Hustlenix/Nightwave/docs/expanded-software-checkpoint.md

# Final-master execution checkpoint

2026-10-03 current continuation: BM83SM1-00TA and Waveshare 24382 non-touch selected.
BD-16 selects TCA9535PWR input expansion; combined map and reviewed charger/pack/
BT rail remain open. The
following historical ledger is superseded for MP3 duration/sparse seek, portable
BT/power/display interfaces and engineering JSON by mp3-seek-index.md and
software-interfaces.md. Actual current-revision CI is in software-validation.md.

2026-10-01. This document is a completion ledger, not a claim that everything
is finished. Existing history is preserved. No final hardware source was
AI-authored, no orders were placed and no human hours/results were invented.

| Requested feature | Actual checkpoint | Remaining acceptance |
| --- | --- | --- |
| Direct microSD MP3/WAV | Existing real three-task engine retained | Real SD/decoder/output latency and hot-remove recovery |
| Lyrics | Bounded LRC loader and current/next OLED view; sample clock | Acoustic alignment, wrapping/Unicode on chosen display |
| Metadata | ID3v2.3/v2.4/v1 and WAV INFO; PCM duration | MP3 duration/index, unsupported tag variants |
| Library | Idle-built SD catalog, 16-row pages, PSRAM artist/album lookup and direct filtered track access; folder/M3U | Metadata reuse; slow fallback/SD contention and real card latency acceptance |
| Modes | Normal/shuffle/repeat-all/repeat-track; EOF advance | Long on-board mixed-media stress |
| Resume | Checked NVS; explicit M3U/folder/index context; checked ordinal hint, legacy/stale fallback | Fast MP3 seek, browser cursor, missing-cache context reconstruction |
| Sleep | Off/15/30/45/60/end-track; pause ramp, stop, display sleep | Measured low power / physical master shutdown |
| Outputs | Speaker/wired/auto preference, faded switch | Chosen Bluetooth transport; actual jack circuit |
| Battery | Unknown/unmeasured displayed honestly | Gauge/bus HAL, charging/fault/low-battery shutdown after power choice |
| Diagnostics | JSON boot/stream/performance/self-test + parser | Task CPU, route counters, BT/battery telemetry, physical evidence |
| Display | Bench OLED; selected 24382 geometry/tile contract | Combined GPIO review, true TFT driver/UI/glyph/current/fit testing |
| Engineering/manufacturing | Updated budgets and source-review gates | Complete BOM, builder sources, ERC/DRC/fit/exports, human review |

## Current validation

At 35b7ab4: [device build](https://github.com/Hustlenix/Nightwave/actions/runs/36878328683)
and [Project quality](https://github.com/Hustlenix/Nightwave/actions/runs/36878328795)
succeeded. Seven suites passed in Release and again with AddressSanitizer/leak
detection, including actual LRC/metadata/playlist sources and 1000 parser/shuffle
cycles. Original fixtures are generated locally/in CI, never copyrighted songs
or lyrics. Host scheduling/drivers are simulated, not hardware measurements.

Later source changes require their own successful run; see software-validation.md.
The 2026-10-02 catalog continuation is described in library-index.md; its source
requires a new device/host run before reusing the older validation claims below.
At 630e3ec device compilation passed; its new playlist-resume assertion failed
with a noncanonical host fixture root. Canonicalised fixtures and isolated
generated-playlist cleanup address that regression; rerun evidence is recorded
only after execution. A targeted frontend test also passed locally in Ubuntu WSL.

Latest validated source: 50df90c device build/size reports and 92c17ea Project
quality, both successful. Seven Release + seven ASAN/leak suites passed. The
targeted frontend/media suites passed ASAN/leak detection locally in WSL too.
See software-validation.md for exact run links and limits; firmware source has
not changed after 50df90c. Future documentation-only evidence commits do not
change the built firmware.
Initial 54ba552 tests caught corrupt-path display clipping; repaired in 35b7ab4.
Do not hide a failed run or treat an unexecuted checklist as a pass.

Current 2026-10-02 checkpoint: 14b10c0 [device build/size](https://github.com/Hustlenix/Nightwave/actions/runs/36962788706)
and [8/8 Release + 8/8 ASAN/leak suites](https://github.com/Hustlenix/Nightwave/actions/runs/36962788677)
passed. This supersedes the older firmware-source/evidence paragraph above.
The catalog and real frontend integrate >128-track fixtures, full indexed/filter
queues and resume. Later v2 lookup source has separate evidence in
software-validation.md; old slow scans remain a declared fallback, not the
normal accelerated group/filter path.
No physical SD, acoustic, battery or hardware-authorship result follows from CI.

## Actual next human gate

BD-14 selects S3 + BM83SM1-00TA, BD-15 selects Waveshare 24382 non-touch and
BD-16 selects TCA9535PWR input expansion. The choices are recorded, but final
schematic/PCB/CAD cannot start until current software is pushed/verified and the
combined numbered map, power/charger/pack/BT rail and support BOM are reviewed.
Selected SKU does not mean functioning radio/display or reviewed drawing.

After the recorded BD-15 choice: reconcile GPIO/SRAM/PSRAM/power and implement exact selected
adapters/display UI. MP3 duration/seek and portable HAL contracts are implemented;
vendor firmware access, rate conversion and physical power adapters remain open. Then
builder authors one subsystem at a time using builder-tasks.md. Reviews identify
specific issues, builder fixes and returns sources; independent human review
and actual manufacturing exports remain hard funding blockers.
