Hustlenix/Nightwave/docs/pixl-funding-readiness.md

# Pixl design/funding requirements

Checked: 2026-10-02 (Asia/Calcutta). This is a design-stage audit, not approval.

Official sources:

- https://pixl.hackclub.com/docs/hardware-requirements
- https://pixl.hackclub.com/docs/submitting
- https://pixl.hackclub.com/docs/first-project
- https://pixl.hackclub.com/docs/sidequest
- https://pixl.hackclub.com/docs/shipping

## Required before design/funding submission

The hardware-specific page distinguishes digital design funding from later build
submission. It requires an understandable README, assembly/PCB images, a finished
replicable design, complete electronics-inclusive CAD with real attachment
methods, firmware source even if untested, linked BOM CSV with total, PCB sources,
STEP and editable CAD sources, and organized relevant files. Another person must
sanity-check the design and their findings must be addressed.

Authorship is mandatory: the design must be original and by the builder, not AI.
The page warns fully AI-generated design files may be permanently rejected.
AI disclosure and clicking approval on AI output cannot be assumed sufficient.
Builder-created electrical/mechanical work and its provenance are still needed;
obtain program guidance if the proposed assistance boundary is unclear.

2026-10-01 continuation: the builder reports direct clarification from Pixl
permitting AI tutor/second-pair-of-eyes assistance while the builder performs
actual schematic/board engineering and makes final decisions. This is reported
by the user, not independently verified correspondence. Follow the specific
builder-authored workflow in builder-tasks.md; research and software continue
while sources are pending. It does not waive source completeness or review.

## Required later for final build submission

The hardware page additionally requires genuine build-progress journals/photos,
finished-build photos and demo video in README, and source changes matching any
assembly bodges. The general submission pages require tracked human work,
journals, demo and AI notes. Do not substitute a design render for a build photo.

## Nightwave status

Public repo verified through GitHub: https://github.com/Hustlenix/Nightwave.
Existing firmware builds and host tests are software evidence only. No physical
playback, runtime, battery/current, thermal or fit results have been returned.

Project URL: https://pixl.hackclub.com/project/1200. The authenticated Chrome
builder session was inspected on 2026-10-02. It is a hardware funding draft with
finished-built-hardware unchecked. Its Trial requires local files, real speakers,
physical playback/volume controls and a full-night battery with actual runtime
stated. The form requires a repo/demo/thumbnail plus BOM CSV, shipping-inclusive
cart images and funding amount. It permits a working link during funding and
requires video for finished hardware. See `project-1200-audit.md` for the separate
funding/build gates and journal-hour correction. No funding submission was made.

## Missing items

A final complete costed BOM and consistent power subsystem;
verified footprints; builder-owned schematic/PCB/CAD; ERC/DRC results; complete
assembly and manufacturing exports; reviewer feedback; complete funding-form
attachments and costs. No funding request is ready or submitted.

## Execution override

The 2026-10-01 funding request supersedes the prior physical-before-digital gate.
Digital software and research proceed while hardware results remain pending.
Paid orders, lithium handling, physical tests, human authorship and independent
sanity checking are not automated or fabricated. A calculated provisional power
model may guide design, but cannot establish measured battery runtime.
