Hustlenix/Nightwave/docs/ai-disclosure.md

# AI Assistance Disclosure

Nightwave uses ChatGPT/Codex for research synthesis, repository organization, documentation drafts, firmware-interface scaffolding, code review, test design, and interpretation of returned measurements.

2026-10-01 funding preparation: Codex also implemented the MP3 framing/adapter,
three-task WAV/MP3 streaming engine, OLED/five-button frontend, NVS volume
persistence, host fakes/regression tests and calculated power model.
AI-written LRC/metadata/playlist parsers, sample clock/seek, playback policies,
versioned settings, JSON diagnostics and PSRAM frontend changes were also added
under the final-master request. Candidate radio/display comparisons and expanded
load scenarios are AI-assisted research/calculations, not builder choices or
bench measurements. These are AI-assisted software/research artifacts, not independently recorded builder
hours or original human-created electrical/mechanical source files. No final
schematic, PCB, enclosure CAD or manufacturing archive was created in this run.

AI output is not physical evidence and is not human engineering time. No AI-generated measurement, runtime, progress photo, journal hour, reviewer feedback, or hardware success claim may be submitted.

2026-10-02 software continuation: Codex authored the bounded SD-backed catalog,
incremental traversal/query state machines, library UI/queue/resume integration,
cache-integrity logic, bounded v2 PSRAM dictionaries/grouped IDs, cache migration,
checked ordinal-hint resume, synthetic tests and accompanying documentation. No
builder radio/display choice, electrical/CAD authorship, physical timing or
independent hardware approval follows from this software work.

Builder-authored continuation (2026-10-01): the builder reports Pixl permits AI
tutoring and second-pair-of-eyes review while the builder performs and owns
schematic/PCB engineering decisions. Codex prepares reference research,
calculations, requirements and review checklists, and reviews returned editable
sources. It does not generate final electrical/mechanical designs wholesale or
write personal decision reasons as if the builder made them. The decision log
records proposals separately from genuine builder selections. No builder
hardware authorship, Hackatime hours or reviewer approval is currently asserted.

The builder is responsible for understanding and materially reviewing the electrical and mechanical design, choosing and purchasing parts, wiring and soldering, performing measurements, maintaining genuine build journals/photos, revising sources to match physical changes, and obtaining a second-person sanity check. PCB and CAD submission files must not be blindly submitted as fully AI-generated work.
