Hustlenix/Nightwave/docs/sanity-check.md

# Independent design sanity check

Status: PENDING; no reviewer or feedback has been supplied.

The review packet is not complete until it links the actual schematic PDF,
PCB front/rear images, full/exploded CAD images, final BOM, power model and pin
map. Existing references are `power-tree.md`, `pin-budget.md`, `risks.md` and
`../hardware/BOM.csv`; these are preliminary, not fabrication approval.

Ask another real person (for example in #pixl) to trace supply limits, battery
polarity/charging/protection, boot straps, bus levels, audio gain/shutdown,
footprints, return paths, connector orientation and mechanical retention.

For each finding retain:

| Actual date | Reviewer | Artifact revision | Finding | Source fix | Verified by |
|---|---|---|---|---|---|

Do not fill this table until a review actually occurs. Resolve findings in source,
regenerate exports, and identify the exact reviewed commit before funding request.
