Hustlenix/Nightwave/hardware/kicad/nightwave-reference/reports/board-bottom.png

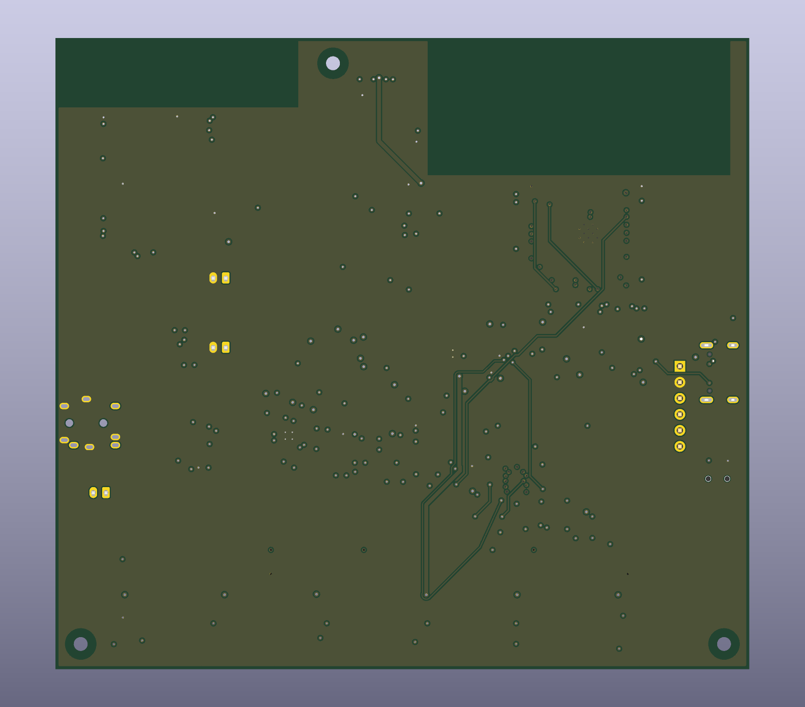
hardware/kicad/nightwave-reference/reports/board-bottom.png
