Hustlenix/Nightwave/hardware/kicad/nightwave-reference/reports/board-top.png

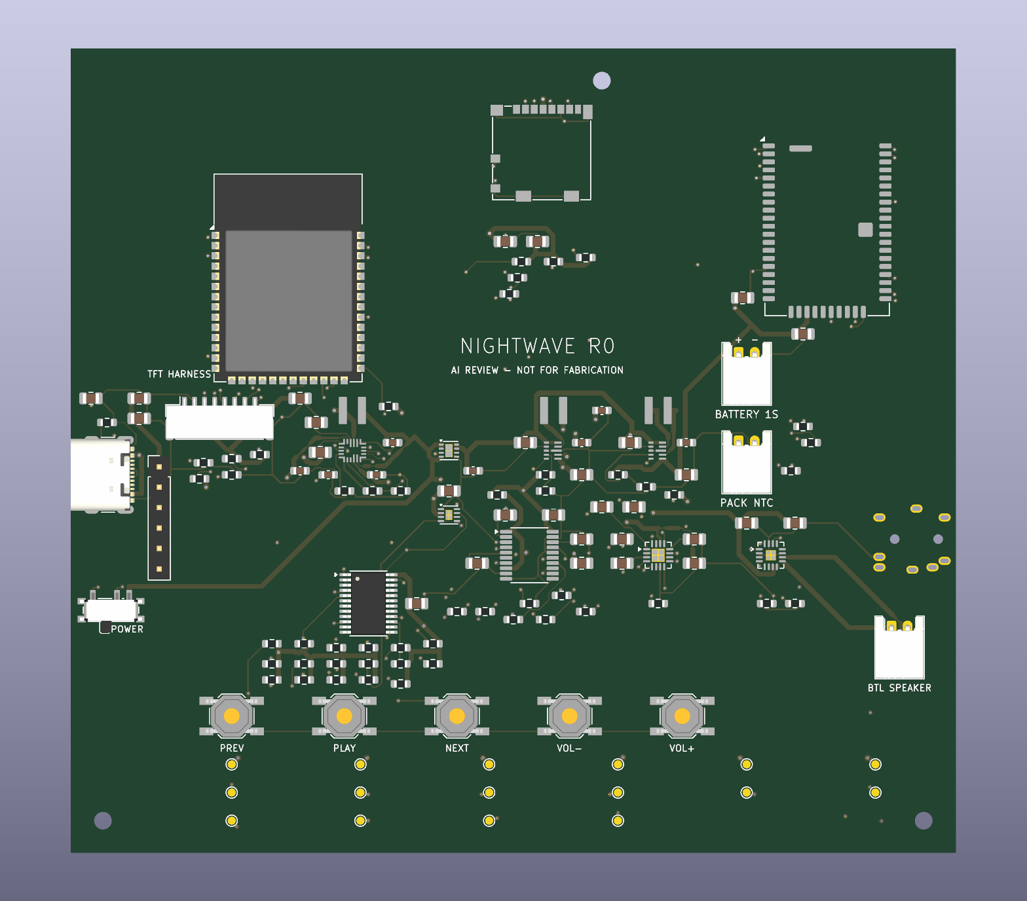
hardware/kicad/nightwave-reference/reports/board-top.png
