Hustlenix/Nightwave/hardware/kicad/nightwave-reference/reports/render/page-7.png

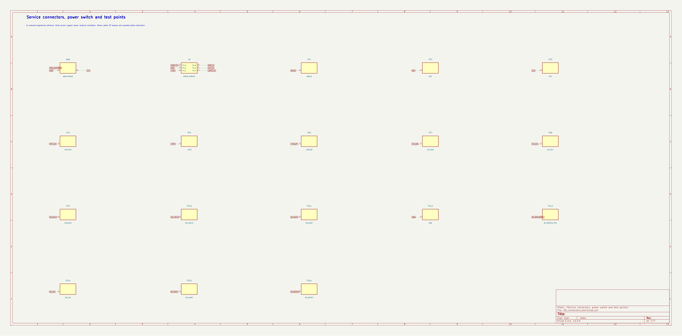
hardware/kicad/nightwave-reference/reports/render/page-7.png
