Hustlenix/Nightwave/hardware/kicad/nightwave-reference/VALIDATION_STATUS.md

# Validation status

Generated UTC: 2026-10-06T04:09:01.274642+00:00

- Components: 135; track/via items: 2436.
- Native KiCad DRC violations: 0.
- Unconnected items: 0.
- Schematic/PCB parity findings: 0.
- ERC uses explicit IC electrical pin types and four supply-source declarations. Zero ERC is **not** analog, mode-configuration or physical qualification.
- 134 power-net segments below 0.6 mm require explicit current-density/voltage-drop review; see `reports/validation.json`. Autorouter necking is not a current-rating approval.
- Gerbers/drills/positions and PCB STEP are review exports only. Missing custom-part 3D bodies are not fit evidence. Board STEP is not enclosure CAD.
- Independent electrical, USB source-current/ESD/impedance, RF, power-loop and mechanical review are pending.
- Exact passive/connector MPNs and complete pricing remain pending; reference BOM is not a complete procurement BOM.
- No physical device, measurements, runtime, assembly photos, demo video or Pixl acceptance is claimed.

**DO NOT FABRICATE OR CONNECT A LITHIUM CELL before closing `REVIEW_CHECKLIST.md`.**
