Hustlenix/Nightwave/tools/analyze_diagnostics.py

"""Read Nightwave JSONL logs without turning missing/host data into bench passes."""
from __future__ import annotations
import argparse
import json
from pathlib import Path

TYPES = {"nightwave_boot", "nightwave_stream", "nightwave_performance", "nightwave_selftest", "nightwave_engineering"}
COUNTERS = {"errors", "underruns", "sd_reads", "decode_calls", "route_changes", "catalog_tracks", "query_reads"}
FLAGS = {"indexed_seek", "catalog_building", "catalog_fast", "bluetooth_backend_ready", "physical_pass"}


def analyze(lines):
    records = []
    for number, line in enumerate(lines, 1):
        if len(line) > 16384:
            raise ValueError(f"line {number}: exceeds 16 KiB")
        # Serial prompts/log prefixes are outside the JSON record.
        opening = line.find("{")
        if opening < 0:
            continue
        try:
            record = json.loads(line[opening:])
        except json.JSONDecodeError:
            continue
        except RecursionError as exc:
            raise ValueError(f"line {number}: excessive JSON nesting") from exc
        if not isinstance(record, dict) or record.get("type") not in TYPES:
            continue
        if type(record.get("schema")) is not int or record.get("schema") != 1:
            raise ValueError(f"line {number}: unsupported schema")
        for key, value in record.items():
            if key == "stack_min_bytes":
                if not isinstance(value, list) or len(value) != 3 or any(type(v) is not int or v < 0 for v in value):
                    raise ValueError(f"line {number}: invalid stack minima")
                continue
            if key in FLAGS and type(value) is not bool:
                raise ValueError(f"line {number}: invalid {key}")
            if key in {"battery_mv", "battery_percent"}:
                maximum = 65535 if key == "battery_mv" else 100
                if value is not None and (type(value) is not int or not 0 <= value <= maximum):
                    raise ValueError(f"line {number}: invalid {key}")
            if key.endswith(("_bytes", "_us", "_ms", "_frames", "_samples")) or key in COUNTERS:
                if type(value) is not int or not 0 <= value <= 0xFFFFFFFF:
                    raise ValueError(f"line {number}: invalid {key}")
        records.append(record)
        if len(records) > 100000:
            raise ValueError("record limit exceeded")
    performance = [r for r in records if r["type"] == "nightwave_performance"]
    summary = {"records": len(records), "physical_acceptance": "NOT_ESTABLISHED", "averages": []}
    engineering = [r for r in records if r["type"] == "nightwave_engineering"]
    if engineering:
        summary["latest_engineering"] = engineering[-1]
    for r in performance:
        sd_time = r.get("sd_total_us", 0)
        calls = r.get("decode_calls", 0)
        reads = r.get("sd_reads", 0)
        saturated = any(r.get(k) == 0xFFFFFFFF for k in ("sd_total_us", "sd_bytes", "decode_total_us"))
        summary["averages"].append({
            "sd_average_us": sd_time / reads if reads and not saturated else None,
            "sd_bytes_per_second": r.get("sd_bytes", 0) * 1_000_000 / sd_time if sd_time and not saturated else None,
            "instrumented_decode_average_us": r.get("decode_total_us", 0) / calls if calls and not saturated else None,
            "counters_saturated": saturated,
        })
    return summary


def self_test():
    assert analyze(["not JSON"]) == {"records": 0, "physical_acceptance": "NOT_ESTABLISHED", "averages": []}
    sample = {"type": "nightwave_performance", "schema": 1, "sd_reads": 2,
              "sd_bytes": 8192, "sd_total_us": 4000, "decode_calls": 2, "decode_total_us": 1000,
              "stack_min_bytes": [1024, 2048, 1024]}
    result = analyze([json.dumps(sample)])
    assert result["averages"][0]["sd_average_us"] == 2000
    assert result["averages"][0]["sd_bytes_per_second"] == 2048000
    sample["sd_total_us"] = 0xFFFFFFFF
    assert analyze([json.dumps(sample)])["averages"][0]["sd_average_us"] is None
    sample["sd_total_us"] = 4000
    for invalid in (-1, True, "100"):
        sample["sd_reads"] = invalid
        try:
            analyze([json.dumps(sample)])
        except ValueError:
            pass
        else:
            raise AssertionError("invalid numeric counter accepted")
    snapshot = {"type": "nightwave_engineering", "schema": 1, "indexed_seek": True,
                "catalog_tracks": 10000, "query_reads": 16, "seek_base_samples": 100,
                "heap_free_bytes": 65536, "battery_mv": None, "battery_percent": None,
                "bluetooth_backend_ready": False, "physical_pass": False}
    result = analyze([json.dumps(snapshot)])
    assert result["records"] == 1 and result["latest_engineering"] == snapshot
    assert result["physical_acceptance"] == "NOT_ESTABLISHED"
    for key, invalid in (("query_reads", True), ("heap_free_bytes", 0x100000000),
                         ("indexed_seek", 1), ("battery_percent", 101), ("battery_mv", "unknown")):
        bad = dict(snapshot, **{key: invalid})
        try:
            analyze([json.dumps(bad)])
        except ValueError:
            pass
        else:
            raise AssertionError(f"invalid engineering field accepted: {key}")
    snapshot["physical_pass"] = True
    assert analyze([json.dumps(snapshot)])["physical_acceptance"] == "NOT_ESTABLISHED"


def main():
    parser = argparse.ArgumentParser(description=__doc__)
    parser.add_argument("log", type=Path, nargs="?")
    parser.add_argument("--self-test", action="store_true")
    args = parser.parse_args()
    if args.self_test:
        self_test()
        print("Diagnostic parser tests passed (synthetic records, not board evidence)")
    elif args.log:
        with args.log.open(encoding="utf-8", errors="replace") as source:
            print(json.dumps(analyze(source), indent=2))
    else:
        parser.error("provide a log or --self-test")


if __name__ == "__main__":
    main()
